neoisback431/ClaudeToy/src/data.h

#pragma once
#include <Arduino.h>
#include <ArduinoJson.h>
#include "ble_bridge.h"
#include "xfer.h"

struct TamaState {
  uint8_t  sessionsTotal;
  uint8_t  sessionsRunning;
  uint8_t  sessionsWaiting;
  bool     recentlyCompleted;
  uint32_t tokensToday;
  uint32_t lastUpdated;
  char     msg[24];
  bool     connected;
  char     lines[8][92];
  uint8_t  nLines;
  uint16_t lineGen;          // bumps when lines change — lets UI reset scroll
  char     promptId[40];     // pending permission request ID; empty = no prompt
  char     promptTool[20];
  char     promptHint[44];
};

// Extra Claude Code info pushed over USB serial by tools/claudetoy_statusline.py:
//   {"cc":{"m":"Opus 4.5","e":"high","c":42,"h":23,"d":41}}
// m = model, e = effort level, c = context used %, h = 5-hour quota %, d = 7-day quota %
// (-1 = unknown). Kept apart from TamaState so it never affects the Bluetooth link state.
struct CcInfo {
  char     model[16];
  char     effort[8];
  int8_t   ctx, h5, d7;
  uint32_t updatedMs;
};
static CcInfo _cc = { "", "", -1, -1, -1, 0 };
inline const CcInfo& ccInfo() { return _cc; }
// Fresh while updates keep arriving (the status line refreshes every few seconds).
inline bool ccFresh() { return _cc.updatedMs != 0 && (millis() - _cc.updatedMs) <= 1800000; }

// ---------------------------------------------------------------------------
// Three modes, checked in priority order:
//   demo   → auto-cycle fake scenarios every 8s, ignore live data
//   live   → JSON arrived in the last 10s over USB or BT
//   asleep → no data, all zeros, "No Claude connected"
// ---------------------------------------------------------------------------

static uint32_t _lastLiveMs = 0;
static uint32_t _lastBtByteMs = 0;   // hasClient() lies; track actual BT traffic
static bool     _demoMode   = false;
static uint8_t  _demoIdx    = 0;
static uint32_t _demoNext   = 0;

struct _Fake { const char* n; uint8_t t,r,w; bool c; uint32_t tok; };
static const _Fake _FAKES[] = {
  {"asleep",0,0,0,false,0}, {"one idle",1,0,0,false,12000},
  {"busy",4,3,0,false,89000}, {"attention",2,1,1,false,45000},
  {"completed",1,0,0,true,142000},
};

inline void dataSetDemo(bool on) {
  _demoMode = on;
  if (on) { _demoIdx = 0; _demoNext = millis(); }
}
inline bool dataDemo() { return _demoMode; }

inline bool dataConnected() {
  return _lastLiveMs != 0 && (millis() - _lastLiveMs) <= 30000;
}

inline bool dataBtActive() {
  // Desktop's idle keepalive is ~10s; give it 1.5x headroom.
  return _lastBtByteMs != 0 && (millis() - _lastBtByteMs) <= 15000;
}

inline const char* dataScenarioName() {
  if (_demoMode) return _FAKES[_demoIdx].n;
  if (dataConnected()) return dataBtActive() ? "bt" : "usb";
  return "none";
}

// Set true once the bridge sends a time sync — until then the RTC may
// hold whatever was on the coin cell (or 2000-01-01 if it lost power).
static bool _rtcValid = false;
inline bool dataRtcValid() { return _rtcValid; }

static void _applyJson(const char* line, TamaState* out) {
  JsonDocument doc;
  if (deserializeJson(doc, line)) return;
#ifdef BUDDY_DEBUG_LOG
  { // field names only (no content) so we can see which data Claude Desktop sends
    Serial.print("[rx keys]");
    for (JsonPair kv : doc.as<JsonObject>()) { Serial.print(' '); Serial.print(kv.key().c_str()); }
    Serial.println();
  }
#endif
  {
    JsonObject cc = doc["cc"];
    if (!cc.isNull()) {
      strlcpy(_cc.model,  cc["m"] | "", sizeof(_cc.model));
      strlcpy(_cc.effort, cc["e"] | "", sizeof(_cc.effort));
      _cc.ctx = (int8_t)constrain((int)(cc["c"] | -1), -1, 100);
      _cc.h5  = (int8_t)constrain((int)(cc["h"] | -1), -1, 100);
      _cc.d7  = (int8_t)constrain((int)(cc["d"] | -1), -1, 100);
      _cc.updatedMs = millis();
#ifdef BUDDY_DEBUG_LOG
      Serial.printf("[cc] m=%s e=%s c=%d h=%d d=%d\n", _cc.model, _cc.effort, _cc.ctx, _cc.h5, _cc.d7);
#endif
      return;   // not a Bluetooth heartbeat: leave link state alone
    }
  }
  if (xferCommand(doc)) { _lastLiveMs = millis(); return; }

  // Bridge sends {"time":[epoch_sec, tz_offset_sec]}; gmtime_r on the
  // adjusted epoch yields local components including weekday.
  JsonArray t = doc["time"];
  if (!t.isNull() && t.size() == 2) {
    time_t local = (time_t)t[0].as<uint32_t>() + (int32_t)t[1];
    struct tm lt; gmtime_r(&local, &lt);
    RTC_TimeTypeDef tm = { (uint8_t)lt.tm_hour, (uint8_t)lt.tm_min, (uint8_t)lt.tm_sec };
    RTC_DateTypeDef dt = { (uint8_t)lt.tm_wday, (uint8_t)(lt.tm_mon + 1),
                           (uint8_t)lt.tm_mday, (uint16_t)(lt.tm_year + 1900) };
    M5.Rtc.SetTime(&tm);
    M5.Rtc.SetDate(&dt);
    extern uint32_t _clkLastRead;
    _clkLastRead = 0;   // force re-read so _clkDt and _rtcValid agree
    _rtcValid = true;
    _lastLiveMs = millis();
    return;
  }

  out->sessionsTotal     = doc["total"]     | out->sessionsTotal;
  out->sessionsRunning   = doc["running"]   | out->sessionsRunning;
  out->sessionsWaiting   = doc["waiting"]   | out->sessionsWaiting;
  out->recentlyCompleted = doc["completed"] | false;
  uint32_t bridgeTokens = doc["tokens"] | 0;
  if (doc["tokens"].is<uint32_t>()) statsOnBridgeTokens(bridgeTokens);
  out->tokensToday = doc["tokens_today"] | out->tokensToday;
  const char* m = doc["msg"];
  if (m) { strncpy(out->msg, m, sizeof(out->msg)-1); out->msg[sizeof(out->msg)-1]=0; }
  JsonArray la = doc["entries"];
  if (!la.isNull()) {
    uint8_t n = 0;
    for (JsonVariant v : la) {
      if (n >= 8) break;
      const char* s = v.as<const char*>();
      strncpy(out->lines[n], s ? s : "", 91); out->lines[n][91]=0;
      n++;
    }
    if (n != out->nLines || (n > 0 && strcmp(out->lines[n-1], out->msg) != 0)) {
      out->lineGen++;
    }
    out->nLines = n;
  }
  JsonObject pr = doc["prompt"];
  if (!pr.isNull()) {
    const char* pid = pr["id"]; const char* pt = pr["tool"]; const char* ph = pr["hint"];
    strncpy(out->promptId,   pid ? pid : "", sizeof(out->promptId)-1);   out->promptId[sizeof(out->promptId)-1]=0;
    strncpy(out->promptTool, pt  ? pt  : "", sizeof(out->promptTool)-1); out->promptTool[sizeof(out->promptTool)-1]=0;
    strncpy(out->promptHint, ph  ? ph  : "", sizeof(out->promptHint)-1); out->promptHint[sizeof(out->promptHint)-1]=0;
  } else {
    out->promptId[0] = 0; out->promptTool[0] = 0; out->promptHint[0] = 0;
  }
  out->lastUpdated = millis();
  _lastLiveMs = millis();
}

template<size_t N>
struct _LineBuf {
  char buf[N];
  uint16_t len = 0;
  void feed(Stream& s, TamaState* out) {
    while (s.available()) {
      char c = s.read();
      if (c == '\n' || c == '\r') {
        if (len > 0) { buf[len]=0; if (buf[0]=='{') _applyJson(buf, out); len=0; }
      } else if (len < N-1) {
        buf[len++] = c;
      }
    }
  }
};

static _LineBuf<1024> _usbLine, _btLine;

inline void dataPoll(TamaState* out) {
  uint32_t now = millis();

  if (_demoMode) {
    if (now >= _demoNext) { _demoIdx = (_demoIdx + 1) % 5; _demoNext = now + 8000; }
    const _Fake& s = _FAKES[_demoIdx];
    out->sessionsTotal=s.t; out->sessionsRunning=s.r; out->sessionsWaiting=s.w;
    out->recentlyCompleted=s.c; out->tokensToday=s.tok; out->lastUpdated=now;
    out->connected = true;
    snprintf(out->msg, sizeof(out->msg), "demo: %s", s.n);
    return;
  }

  _usbLine.feed(Serial, out);
  // BLE ring buffer is drained manually since it's not a Stream.
  while (bleAvailable()) {
    int c = bleRead();
    if (c < 0) break;
    _lastBtByteMs = millis();
    if (c == '\n' || c == '\r') {
      if (_btLine.len > 0) {
        _btLine.buf[_btLine.len] = 0;
        if (_btLine.buf[0] == '{') _applyJson(_btLine.buf, out);
        _btLine.len = 0;
      }
    } else if (_btLine.len < sizeof(_btLine.buf) - 1) {
      _btLine.buf[_btLine.len++] = (char)c;
    }
  }

  out->connected = dataConnected();
  if (!out->connected) {
    out->sessionsTotal=0; out->sessionsRunning=0; out->sessionsWaiting=0;
    out->recentlyCompleted=false; out->lastUpdated=now;
    strncpy(out->msg, "No Claude connected", sizeof(out->msg)-1);
    out->msg[sizeof(out->msg)-1]=0;
  }
}
